zenitheesc/USPSat-I/Alves_ADC v.1.0/Images/Alves_ADC v.1.0 - Bottom.png

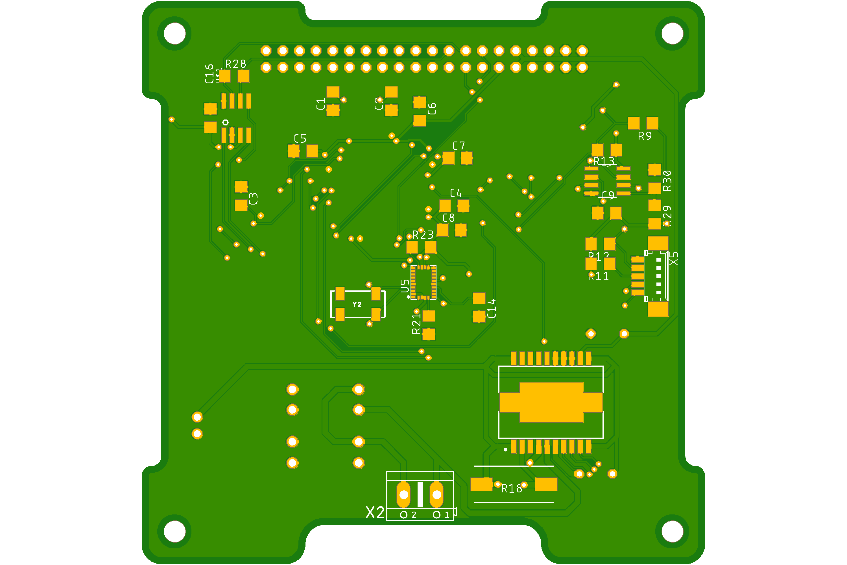
Alves_ADC v.1.0/Images/Alves_ADC v.1.0 - Bottom.png
