zenitheesc/USPSat-I/Alves_ADC v.1.0/Images/Alves_ADC v.1.0 - Top.png

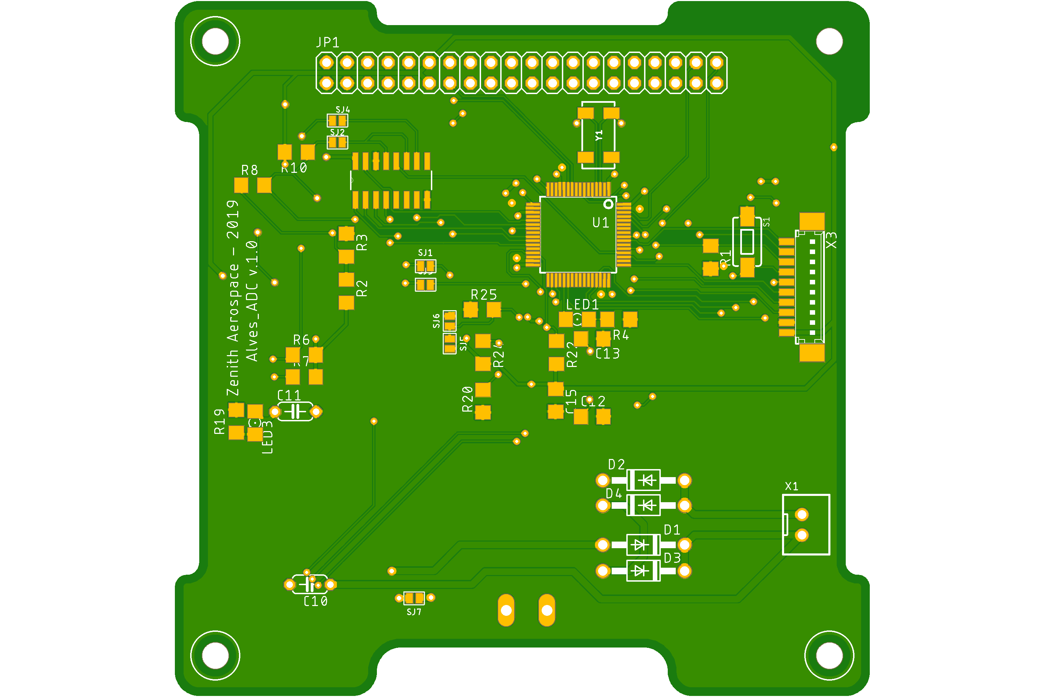
Alves_ADC v.1.0/Images/Alves_ADC v.1.0 - Top.png
