zenitheesc/USPSat-I/Caurin_CDH v.1.0/Images/Caurin_CDH v.1.0 - Bottom.png

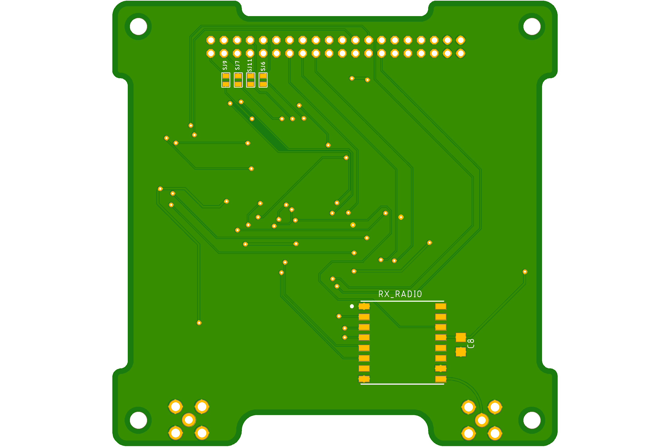
Caurin_CDH v.1.0/Images/Caurin_CDH v.1.0 - Bottom.png
