zenitheesc/USPSat-I/Comin_CTR v.1.0/Images/Comin_CTR v.1.0 - Bottom.png

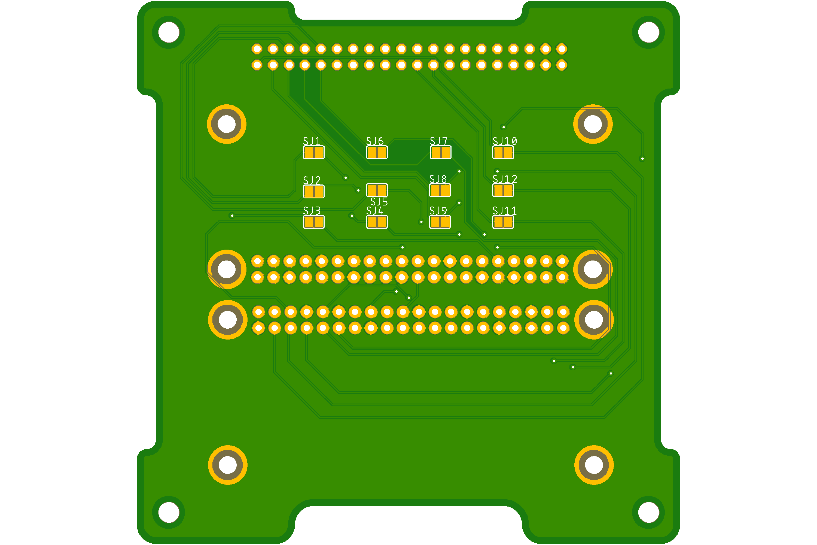
Comin_CTR v.1.0/Images/Comin_CTR v.1.0 - Bottom.png
